federicogramos/pk2/pcb/pk2/otherFiles/WEBDOC_IX00000002_N0002.jpg

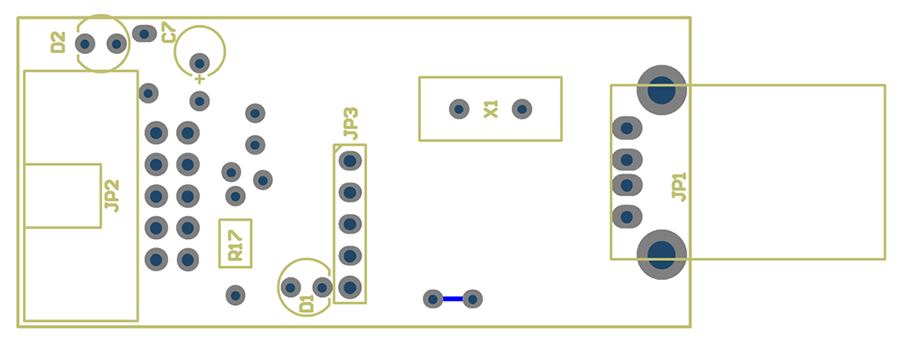
pcb/pk2/otherFiles/WEBDOC_IX00000002_N0002.jpg
